rodan/lemidi/firmware_cpp/drivers/sys_messagebus.cpp

/*
    openchronos system messagebus implementation

         Copyright (C) 2012 Angelo Arrifano <miknix@gmail.com>

                  http://www.openchronos-ng.sourceforge.net

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
    You should have received a copy of the GNU General Public License
    along with this program.  If not, see <http://www.gnu.org/licenses/>.
 */

#include "sys_messagebus.h"

// static 
struct sys_messagebus *messagebus;

struct sys_messagebus * sys_messagebus_getp(void)
{
    return messagebus;
}

void sys_messagebus_register(void (*callback) (const uint16_t sys_message),
                             const uint16_t listens)
{
    struct sys_messagebus **p = &messagebus;

    while (*p) {
        p = &(*p)->next;
    }

    //*p = malloc(sizeof(struct sys_messagebus));
    (*p)->next = NULL;
    (*p)->fn = callback;
    (*p)->listens = listens;
}

void sys_messagebus_unregister(void (*callback) (const uint16_t sys_message))
{
    struct sys_messagebus *p = messagebus, *pp = NULL;

    while (p) {
        if (p->fn == callback) {
            if (!pp)
                messagebus = p->next;
            else
                pp->next = p->next;

            free(p);
        }

        pp = p;
        p = p->next;
    }
}
